sparkjl/TinyMatrix/firmware/Project/APL/apl_key_menu.c

#include "includes.h"

Menu_StateTypeDef menu_state = Menu_R;
uint8_t menu_item = 1;
uint8_t key_value = 0;

void apl_menu_init(void)
{
  apl_menu_r_display((menu_item-1)/3);
}

void apl_menu_handle(void)
{
  key_value = bsp_key_read();

  if(key_value)
  {
    switch(menu_state)
    {

      case Menu_R:
        apl_menu_r_callback();
        break;


      case Menu_M:
        apl_menu_m_callback();
        break;

      case Menu_1:
        apl_menu_1_callback();
        break;

      case Menu_2:
        apl_menu_2_callback();
        break;

      case Menu_3:
        break;

      case Menu_4:
        apl_menu_4_callback();
        break;

      case Menu_1_1:
        apl_menu_1_1_callback();
        break;

      case Menu_4_1:
        apl_menu_4_1_callback();
        break;

      case Menu_4_2:
        apl_menu_4_2_callback();
        break;

      default:
        break;
    }
  }
}

void apl_menu_r_callback(void)
{
  switch(key_value)
  {
    case KEY1_SHORT:
      break;

    case KEY1_LONG:
      break;

    case KEY2_SHORT:
      break;

    case KEY2_LONG:
      break;

    case KEY3_SHORT:
      break;

    case KEY3_LONG:
      menu_state = Menu_M;
      menu_item = 1;
      apl_menu_m_display((menu_item-1)/3);
      api_task_delete(Task_MatrixShift);
      break;

    case KEY4_SHORT:
      break;

    case KEY4_LONG:
      break;

    default:
      break;
  }
}

void apl_menu_r_display(uint8_t page)
{
  apl_font_init();
  apl_font_display(0,  0, HUB75_PANEL_WIDTH, 16, "        ", 16, 0);
  apl_font_display(0, 16, HUB75_PANEL_WIDTH, 16, "        ", 16, 0);
  apl_font_display(0, 32, HUB75_PANEL_WIDTH, 16, "        ", 16, 0);
  apl_font_display(0, 48, HUB75_PANEL_WIDTH, 16, "        ", 16, 0);
}

void apl_menu_m_callback(void)
{

  switch(key_value)
  {
    case KEY1_SHORT:
      if(menu_item-- == 1)
        menu_item = 4;
      apl_menu_m_display((menu_item-1)/3);
      break;

    case KEY1_LONG:
      break;

    case KEY2_SHORT:
      if(menu_item++ == 4)
        menu_item = 1;
      apl_menu_m_display((menu_item-1)/3);
      break;

    case KEY2_LONG:
      break;

    case KEY3_SHORT:
      if(menu_item == 1)
      {
        menu_state = Menu_1;
        menu_item = 1;
        apl_menu_1_display((menu_item-1)/3);
      }
      else if(menu_item == 2)
      {
        menu_state = Menu_2;
        menu_item = 1;
        apl_menu_2_display((menu_item-1)/3);
      }
      else if(menu_item == 3)
      {
      }
      else if(menu_item == 4)
      {
        menu_state = Menu_4;
        menu_item = 1;
        apl_menu_4_display((menu_item-1)/3);
      }
      break;

    case KEY3_LONG:
      break;

    case KEY4_SHORT:
      break;

    case KEY4_LONG:
      menu_state = Menu_R;
      menu_item = 1;
      apl_menu_r_display((menu_item-1)/3);
      api_task_create(Task_MatrixShift, sys_data.shift_period);
      break;

    default:
      break;
  }
}

void apl_menu_m_display(uint8_t page)
{
  apl_font_display(0, 0, HUB75_PANEL_WIDTH, 16, " SET UP ", 16, 0);

  if(page == 0)
  {
    apl_font_display(0, 16, HUB75_PANEL_WIDTH, 16, "1.Font  ", 16, 0);
    apl_font_display(0, 32, HUB75_PANEL_WIDTH, 16, "2.Color ", 16, 0);
    apl_font_display(0, 48, HUB75_PANEL_WIDTH, 16, "3.Lang  ", 16, 0);
    apl_font_reverse(0, menu_item*16, HUB75_PANEL_WIDTH, 16);
  }
  else if(page == 1)
  {
    apl_font_display(0, 16, HUB75_PANEL_WIDTH, 16, "4.Freq  ", 16, 0);
    apl_font_display(0, 32, HUB75_PANEL_WIDTH, 16, "        ", 16, 0);
    apl_font_display(0, 48, HUB75_PANEL_WIDTH, 16, "        ", 16, 0);
    apl_font_reverse(0, (menu_item-3)*16, HUB75_PANEL_WIDTH, 16);
  }
}

void apl_menu_1_callback(void)
{

  switch(key_value)
  {
    case KEY1_SHORT:
      if(menu_item-- == 1)
        menu_item = 3;
      apl_menu_1_display((menu_item-1)/3);
      break;

    case KEY1_LONG:
      break;

    case KEY2_SHORT:
      if(menu_item++ == 3)
        menu_item = 1;
      apl_menu_1_display((menu_item-1)/3);
      break;

    case KEY2_LONG:
      break;

    case KEY3_SHORT:
      if(menu_item == 1)
      {
        font_size = 12;
      }
      else if(menu_item == 2)
      {
        font_size = 16;
      }
      else if(menu_item == 3)
      {
        font_size = 24;
      }
      menu_state = Menu_1_1;
      menu_item = 1;
      apl_menu_1_1_display((menu_item-1)/3);
      break;

    case KEY3_LONG:
      break;

    case KEY4_SHORT:
        menu_state = Menu_M;
        menu_item = 1;
        apl_menu_m_display((menu_item-1)/3);
        font_mode = 0;
      break;

    case KEY4_LONG:
      break;

    default:
      break;
  }
}

void apl_menu_1_display(uint8_t page)
{
  apl_font_display(0, 0, HUB75_PANEL_WIDTH, 16, "  FONT  ", 16, 0);

  if(page == 0)
  {
    apl_font_display(0, 16, HUB75_PANEL_WIDTH, 16, "1.Font12", 16, 0);
    apl_font_display(0, 32, HUB75_PANEL_WIDTH, 16, "2.Font16", 16, 0);
    apl_font_display(0, 48, HUB75_PANEL_WIDTH, 16, "3.Font24", 16, 0);
    apl_font_reverse(0, menu_item*16, HUB75_PANEL_WIDTH, 16);
  }
}

void apl_menu_2_callback(void)
{

  switch(key_value)
  {
    case KEY1_SHORT:
      if(menu_item-- == 1)
        menu_item = 9;
      apl_menu_2_display((menu_item-1)/3);
      break;

    case KEY1_LONG:
      break;

    case KEY2_SHORT:
      if(menu_item++ == 9)
        menu_item = 1;
      apl_menu_2_display((menu_item-1)/3);
      break;

    case KEY2_LONG:
      break;

    case KEY3_SHORT:
      if(menu_item == 1)
      {
        hub75_color = HUB75_Color_Red;
        hub75_blink = 0;
      }
      else if(menu_item == 2)
      {
        hub75_color = HUB75_Color_Green;
        hub75_blink = 0;
      }
      else if(menu_item == 3)
      {
        hub75_color = HUB75_Color_Yellow;
        hub75_blink = 0;
      }
      else if(menu_item == 4)
      {
        hub75_color = HUB75_Color_Blue;
        hub75_blink = 0;
      }
      else if(menu_item == 5)
      {
        hub75_color = HUB75_Color_Pink;
        hub75_blink = 0;
      }
      else if(menu_item == 6)
      {
        hub75_color = HUB75_Color_Cyan;
        hub75_blink = 0;
      }
      else if(menu_item == 7)
      {
        hub75_color = HUB75_Color_White;
        hub75_blink = 0;
      }
      else if(menu_item == 8)
      {
        hub75_color = HUB75_Color_Black;
        hub75_blink = 1;
      }
      else if(menu_item == 9)
      {
        apl_font_display(0,  0, HUB75_PANEL_WIDTH, 12, "Spark Zheng", 12, 0);
        apl_font_display(0, 12, HUB75_PANEL_WIDTH, 12, "Led Matrix", 12, 0);
        apl_font_display(0, 24, HUB75_PANEL_WIDTH, 16, "WellDone", 16, 0);
        apl_font_display(0, 40, HUB75_PANEL_WIDTH, 24, "Fight!", 24, 0);
      }
      sys_data.display_color = hub75_color;
      break;

    case KEY3_LONG:
      break;

    case KEY4_SHORT:
        menu_state = Menu_M;
        menu_item = 1;
        apl_menu_m_display((menu_item-1)/3);
      break;

    case KEY4_LONG:
      break;

    default:
      break;
  }
}

void apl_menu_2_display(uint8_t page)
{
  apl_font_display(0, 0, HUB75_PANEL_WIDTH, 16, "  COLOR ", 16, 0);

  if(page == 0)
  {
    apl_font_display(0, 16, HUB75_PANEL_WIDTH, 16, "1.Red   ", 16, 0);
    apl_font_display(0, 32, HUB75_PANEL_WIDTH, 16, "2.Green ", 16, 0);
    apl_font_display(0, 48, HUB75_PANEL_WIDTH, 16, "3.Yellow", 16, 0);
    apl_font_reverse(0, (menu_item)*16, HUB75_PANEL_WIDTH, 16);
  }
  else if(page == 1)
  {
    apl_font_display(0, 16, HUB75_PANEL_WIDTH, 16, "4.Blue  ", 16, 0);
    apl_font_display(0, 32, HUB75_PANEL_WIDTH, 16, "5.Pink  ", 16, 0);
    apl_font_display(0, 48, HUB75_PANEL_WIDTH, 16, "6.Cyan  ", 16, 0);
    apl_font_reverse(0, (menu_item-3)*16, HUB75_PANEL_WIDTH, 16);
  }
  else if(page == 2)
  {
    apl_font_display(0, 16, HUB75_PANEL_WIDTH, 16, "7.White ", 16, 0);
    apl_font_display(0, 32, HUB75_PANEL_WIDTH, 16, "8.Auto  ", 16, 0);
    apl_font_display(0, 48, HUB75_PANEL_WIDTH, 16, "        ", 16, 0);
    apl_font_reverse(0, (menu_item-6)*16, HUB75_PANEL_WIDTH, 16);
  }
}

void apl_menu_4_callback(void)
{

  switch(key_value)
  {
    case KEY1_SHORT:
      if(menu_item-- == 1)
        menu_item = 2;
      apl_menu_4_display((menu_item-1)/3);
      break;

    case KEY1_LONG:
      break;

    case KEY2_SHORT:
      if(menu_item++ == 2)
        menu_item = 1;
      apl_menu_4_display((menu_item-1)/3);
      break;

    case KEY2_LONG:
      break;

    case KEY3_SHORT:
      if(menu_item == 1)
      {
        menu_state = Menu_4_1;
        menu_item = 1;
        apl_menu_4_1_display((menu_item-1)/3);
      }
      else if(menu_item == 2)
      {
        menu_state = Menu_4_2;
        menu_item = 1;
        apl_menu_4_2_display((menu_item-1)/3);
      }
      break;

    case KEY3_LONG:
      break;

    case KEY4_SHORT:
        menu_state = Menu_M;
        menu_item = 1;
        apl_menu_m_display((menu_item-1)/3);
        font_mode = 0;
      break;

    case KEY4_LONG:
      break;

    default:
      break;
  }
}

void apl_menu_4_display(uint8_t page)
{
  apl_font_display(0, 0, HUB75_PANEL_WIDTH, 16, "  FREQ  ", 16, 0);

  if(page == 0)
  {
    apl_font_display(0, 16, HUB75_PANEL_WIDTH, 16, "1.D_freq", 16, 0);
    apl_font_display(0, 32, HUB75_PANEL_WIDTH, 16, "2.S_peri", 16, 0);
    apl_font_display(0, 48, HUB75_PANEL_WIDTH, 16, "        ", 16, 0);
    apl_font_reverse(0, menu_item*16, HUB75_PANEL_WIDTH, 16);
  }
}

void apl_menu_1_1_callback(void)
{

  switch(key_value)
  {
    case KEY1_SHORT:
      if(menu_item-- == 1)
        menu_item = 3;
      apl_menu_1_1_display((menu_item-1)/3);
      break;

    case KEY1_LONG:
      break;

    case KEY2_SHORT:
      if(menu_item++ == 3)
        menu_item = 1;
      apl_menu_1_1_display((menu_item-1)/3);
      break;

    case KEY2_LONG:
      break;

    case KEY3_SHORT:
      if(menu_item == 1)
      {
        font_mode = 0;
        apl_font_display(0, 16, HUB75_PANEL_WIDTH, 16, "< < Dis ", 16, 0);
        sys_data.font_size = font_size;
      }
      else if(menu_item == 2)
      {
        font_mode = 1;
        apl_font_display(0, 32, HUB75_PANEL_WIDTH, 16, " Upg > >", 16, 0);
      }
      else if(menu_item == 3)
      {
        font_mode = 2;
        apl_font_display(0, 48, HUB75_PANEL_WIDTH, 16, "Erasing.", 16, 0);
        if(font_size == 12)
          apl_font_erase(0);
        else if(font_size == 16)
          apl_font_erase(1);
        else if(font_size == 24)
          apl_font_erase(2);
        apl_font_display(0, 48, HUB75_PANEL_WIDTH, 16, "Era Done", 16, 0);
      }
      break;

    case KEY3_LONG:
      break;

    case KEY4_SHORT:
      menu_state = Menu_1;
      menu_item = 1;
      apl_menu_1_display((menu_item-1)/3);
      break;

    case KEY4_LONG:
      break;

    default:
      break;
  }
}

void apl_menu_1_1_display(uint8_t page)
{
  uint8_t dis_str[20];

  sprintf((char*)dis_str, " FONT%2d ", font_size);
  apl_font_display(0, 0, HUB75_PANEL_WIDTH, 16, dis_str, 16, 0);
  if(page == 0)
  {
    apl_font_display(0, 16, HUB75_PANEL_WIDTH, 16, "1.SEL. *", 16, 0);
    apl_font_display(0, 32, HUB75_PANEL_WIDTH, 16, "2.UPG. *", 16, 0);
    apl_font_display(0, 48, HUB75_PANEL_WIDTH, 16, "3.EAU. !", 16, 0);
    apl_font_reverse(0, menu_item*16, HUB75_PANEL_WIDTH, 16);
  }
}

void apl_menu_4_1_callback(void)
{
  if(sys_data.display_freq % 60)
    sys_data.display_freq = 60;

  switch(key_value)
  {
    case KEY1_SHORT:
      if(sys_data.display_freq == 60)
        sys_data.display_freq = 900;
      else
        sys_data.display_freq -= 60;
      apl_menu_4_1_display((menu_item-1)/3);
      break;

    case KEY1_LONG:
      break;

    case KEY2_SHORT:
      if(sys_data.display_freq == 900)
        sys_data.display_freq = 60;
      else
        sys_data.display_freq += 60;
      apl_menu_4_1_display((menu_item-1)/3);
      break;

    case KEY2_LONG:
      break;

    case KEY3_SHORT:
      break;

    case KEY3_LONG:
      break;

    case KEY4_SHORT:
        menu_state = Menu_4;
        menu_item = 1;
        apl_menu_4_display((menu_item-1)/3);
      break;

    case KEY4_LONG:
      break;

    default:
      break;
  }
}

void apl_menu_4_1_display(uint8_t page)
{
  uint8_t dis_str[20];

  sprintf((char*)dis_str, " %3d Hz ", sys_data.display_freq);
  apl_font_display(0, 0, HUB75_PANEL_WIDTH, 16, "Dis_Freq", 16, 0);
  if(page == 0)
  {
    apl_font_display(0, 16, HUB75_PANEL_WIDTH, 16, dis_str, 16, 0);
    apl_font_display(0, 32, HUB75_PANEL_WIDTH, 16, "        ", 16, 0);
    apl_font_display(0, 48, HUB75_PANEL_WIDTH, 16, "        ", 16, 0);
    apl_font_reverse(0, menu_item*16, HUB75_PANEL_WIDTH, 16);
  }
}

void apl_menu_4_2_callback(void)
{
  if(sys_data.shift_period % 10)
    sys_data.shift_period = 10;

  switch(key_value)
  {
    case KEY1_SHORT:
      if(sys_data.shift_period == 10)
        sys_data.shift_period = 900;
      else
        sys_data.shift_period -= 10;
      apl_menu_4_2_display((menu_item-1)/3);
      break;

    case KEY1_LONG:
      break;

    case KEY2_SHORT:
      if(sys_data.shift_period == 900)
        sys_data.shift_period = 10;
      else
        sys_data.shift_period += 10;
      apl_menu_4_2_display((menu_item-1)/3);
      break;

    case KEY2_LONG:
      break;

    case KEY3_SHORT:
      break;

    case KEY3_LONG:
      break;

    case KEY4_SHORT:
        menu_state = Menu_4;
        menu_item = 1;
        apl_menu_4_display((menu_item-1)/3);
      break;

    case KEY4_LONG:
      break;

    default:
      break;
  }
}
void apl_menu_4_2_display(uint8_t page)
{
  uint8_t dis_str[20];

  sprintf((char*)dis_str, " %3d ms ", sys_data.shift_period);
  apl_font_display(0, 0, HUB75_PANEL_WIDTH, 16, "Shi_Peri", 16, 0);
  if(page == 0)
  {
    apl_font_display(0, 16, HUB75_PANEL_WIDTH, 16, dis_str, 16, 0);
    apl_font_display(0, 32, HUB75_PANEL_WIDTH, 16, "        ", 16, 0);
    apl_font_display(0, 48, HUB75_PANEL_WIDTH, 16, "        ", 16, 0);
    apl_font_reverse(0, menu_item*16, HUB75_PANEL_WIDTH, 16);
  }
}
