sparkjl/TinyMatrix/firmware/Project/APL/apl_uart_link.c

#include "includes.h"

//#define CRC16_BUYPASS      1
#define CRC16_MODBUS       2

#ifdef CRC16_BUYPASS
/* CRC-16/BUYPASS width=16 poly=0x8005 init=0x0000 refin=false refout=false xorout=0x0000 */

static const uint16_t crc16_table[256] = {
0x0000,0x8005,0x800F,0x000A,0x801B,0x001E,0x0014,0x8011,
0x8033,0x0036,0x003C,0x8039,0x0028,0x802D,0x8027,0x0022,
0x8063,0x0066,0x006C,0x8069,0x0078,0x807D,0x8077,0x0072,
0x0050,0x8055,0x805F,0x005A,0x804B,0x004E,0x0044,0x8041,
0x80C3,0x00C6,0x00CC,0x80C9,0x00D8,0x80DD,0x80D7,0x00D2,
0x00F0,0x80F5,0x80FF,0x00FA,0x80EB,0x00EE,0x00E4,0x80E1,
0x00A0,0x80A5,0x80AF,0x00AA,0x80BB,0x00BE,0x00B4,0x80B1,
0x8093,0x0096,0x009C,0x8099,0x0088,0x808D,0x8087,0x0082,
0x8183,0x0186,0x018C,0x8189,0x0198,0x819D,0x8197,0x0192,
0x01B0,0x81B5,0x81BF,0x01BA,0x81AB,0x01AE,0x01A4,0x81A1,
0x01E0,0x81E5,0x81EF,0x01EA,0x81FB,0x01FE,0x01F4,0x81F1,
0x81D3,0x01D6,0x01DC,0x81D9,0x01C8,0x81CD,0x81C7,0x01C2,
0x0140,0x8145,0x814F,0x014A,0x815B,0x015E,0x0154,0x8151,
0x8173,0x0176,0x017C,0x8179,0x0168,0x816D,0x8167,0x0162,
0x8123,0x0126,0x012C,0x8129,0x0138,0x813D,0x8137,0x0132,
0x0110,0x8115,0x811F,0x011A,0x810B,0x010E,0x0104,0x8101,
0x8303,0x0306,0x030C,0x8309,0x0318,0x831D,0x8317,0x0312,
0x0330,0x8335,0x833F,0x033A,0x832B,0x032E,0x0324,0x8321,
0x0360,0x8365,0x836F,0x036A,0x837B,0x037E,0x0374,0x8371,
0x8353,0x0356,0x035C,0x8359,0x0348,0x834D,0x8347,0x0342,
0x03C0,0x83C5,0x83CF,0x03CA,0x83DB,0x03DE,0x03D4,0x83D1,
0x83F3,0x03F6,0x03FC,0x83F9,0x03E8,0x83ED,0x83E7,0x03E2,
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
    {
      ulink.data[i] = uart1.rx_buff[4+i];
    }

    ulink.crc16[0] = uart1.rx_buff[ulink.length+4];
    ulink.crc16[1] = uart1.rx_buff[ulink.length+5];

    api_uart_rx_start(&uart1);

    crc_code = crc16_create((uint8_t *)&ulink, ulink.length+4);

    if((ulink.crc16[0] == (crc_code & 0xff)) && (ulink.crc16[1] == (crc_code >> 8)))
    {
      status = 1;
      if(ulink.addr == 0x01)
      {
        status = 2;
        switch(ulink.func)
        {
          case 0x00:
            break;

          case 0x01:
            apl_font_upgrade(ulink.data, ulink.length);
            break;

          case 0x10:
          case 0x11:
          case 0x12:
          case 0x13:
          case 0x14:
          case 0x15:
            strcpy((char*)sys_data.font_text[ulink.func & 0x0f], (char*)ulink.data);
            break;

          default:
            break;
        }

        if(ulink.func == 0x01)
        {
          uart1.tx_buff[0] = ulink.addr;
          uart1.tx_buff[1] = ulink.func;
          uart1.tx_buff[2] = ulink.tick;
          uart1.tx_buff[3] = ulink.length = 0;

          crc16_fill(uart1.tx_buff, 6);
          api_uart_tx_start(&uart1, uart1.tx_buff, 6);
        }
        else
        {
          uart1.tx_buff[0] = ulink.addr;
          uart1.tx_buff[1] = ulink.func;
          uart1.tx_buff[2] = ulink.tick;
          uart1.tx_buff[3] = ulink.length;

          for(uint16_t i=0; i<ulink.length; i++)
          {
            uart1.tx_buff[4+i] = ulink.data[i];
          }

          crc16_fill(uart1.tx_buff, ulink.length+6);
          api_uart_tx_start(&uart1, uart1.tx_buff, ulink.length+6);
        }
      }
    }
  }

  return status;
}
