sparkjl/TinyMatrix/firmware/Project/APL/apl_task.h

#ifndef __APL_TASK_H_
#define __APL_TASK_H_

void Task_Handle(void);
void Task_Start(void);

void Task_SysdataHandle(void);
void Task_MatrixDisplay(void);
void Task_MatrixTest(void);
void Task_LED1(void);
void Task_KeyScan(void);
void Task_MatrixBlink(void);
void Task_MatrixShift(void);
void Task_MenuHandle(void);
void Task_FontHandle(void);
void Task_UartTx(void);

#endif /* __APL_TASK_H_ */
