sparkjl/TinyMatrix/firmware/Project/API/api_spi.h

#ifndef __API_SPI_H_
#define __API_SPI_H_

/* SPI1 CS */
#define SPI1_CS1_H()            HAL_GPIO_WritePin(GPIOC, GPIO_PIN_3, GPIO_PIN_SET)
#define SPI1_CS1_L()            HAL_GPIO_WritePin(GPIOC, GPIO_PIN_3, GPIO_PIN_RESET)
#define SPI1_CS2_H()            HAL_GPIO_WritePin(GPIOC, GPIO_PIN_4, GPIO_PIN_SET)
#define SPI1_CS2_L()            HAL_GPIO_WritePin(GPIOC, GPIO_PIN_4, GPIO_PIN_RESET)
#define SPI1_CS3_H()            HAL_GPIO_WritePin(GPIOC, GPIO_PIN_5, GPIO_PIN_SET)
#define SPI1_CS3_L()            HAL_GPIO_WritePin(GPIOC, GPIO_PIN_5, GPIO_PIN_RESET)

/* SPI2 CS */
#define SPI2_CS0_H()            HAL_GPIO_WritePin(GPIOB, GPIO_PIN_12, GPIO_PIN_SET)
#define SPI2_CS0_L()            HAL_GPIO_WritePin(GPIOB, GPIO_PIN_12, GPIO_PIN_RESET)
#define SPI2_CS1_H()            HAL_GPIO_WritePin(GPIOB, GPIO_PIN_2, GPIO_PIN_SET)
#define SPI2_CS1_L()            HAL_GPIO_WritePin(GPIOB, GPIO_PIN_2, GPIO_PIN_RESET)
#define SPI2_CS2_H()            HAL_GPIO_WritePin(GPIOC, GPIO_PIN_8, GPIO_PIN_SET)
#define SPI2_CS2_L()            HAL_GPIO_WritePin(GPIOC, GPIO_PIN_8, GPIO_PIN_RESET)
#define SPI2_CS3_H()            HAL_GPIO_WritePin(GPIOC, GPIO_PIN_1, GPIO_PIN_SET)
#define SPI2_CS3_L()            HAL_GPIO_WritePin(GPIOC, GPIO_PIN_1, GPIO_PIN_RESET)
#define SPI2_RST_H()            HAL_GPIO_WritePin(GPIOB, GPIO_PIN_7, GPIO_PIN_SET)
#define SPI2_RST_L()            HAL_GPIO_WritePin(GPIOB, GPIO_PIN_7, GPIO_PIN_RESET)

extern SPI_HandleTypeDef hspi1;
extern SPI_HandleTypeDef hspi2;
extern SPI_HandleTypeDef hspi3;

void api_spi_init(void);

#endif /* __API_SPI_H_ */
